Jconn/Fedora_Repo/MAAV_Projects/Spine/14v0/modules/Logic_Level_Bidirectional.sch

## EAGLE design MAAV_Projects/Spine/14v0/modules/Logic_Level_Bidirectional.sch (2014-05-22)

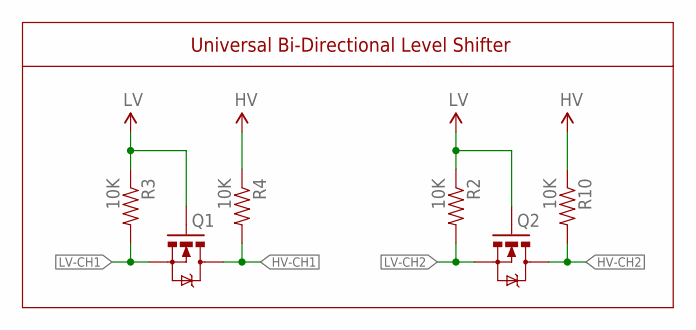
[picture p34: schematic Logic_Level_Bidirectional.sch]

Parts:
Q1: BSS138; SOT23; DIGIKEY BSS138KCT-ND
Q2: MOSFET-NCHANNELBSS138; SOT23; DIGIKEY BSS138KCT-ND
R2, R3, R4, R10: 10K; 0603-RES; DIGIKEY RMCF0603JT10K0CT-ND

Connections:
HV: R4.1, R10.1
HV-CH1: Q1.3 (D), R4.2
HV-CH2: Q2.3 (D), R10.2
LV: Q1.1 (G), Q2.1 (G), R2.1, R3.1
LV-CH1: Q1.2 (S), R3.2
LV-CH2: Q2.2 (S), R2.2

Notes on the sheet:
Universal Bi-Directional Level Shifter
