Jconn/Fedora_Repo/MAAV_Projects/Spine/14v0/modules/Motor Ouptut.sch

## EAGLE design MAAV_Projects/Spine/14v0/modules/Motor Ouptut.sch (2014-05-22)

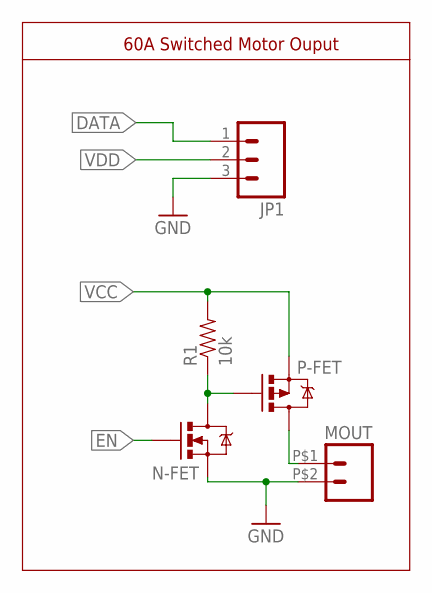
[picture p35: schematic Motor Ouptut.sch]

Parts:
JP1: M03PTH; 1X03; DIGIKEY 952-2264-ND
MOUT: MINI_FIT_JR_5569; MINI_FIT_JR
N-FET: MOSFET-NCHANNELBSS138; SOT23; DIGIKEY BSS138KCT-ND
P-FET: MOSFET_P-CHANNEL; POWERPAK_SO-8_SINGLE; DIGIKEY SI7135DP-T1-GE3CT-ND
R1: 10k; 0603-RES; DIGIKEY RMCF0603JT10K0CT-ND

Connections:
DATA: JP1.1
EN: N-FET.1 (G)
GND: JP1.3
unnamed: MOUT.P$1 (2), P-FET.P$5 (D)
unnamed: N-FET.3 (D), P-FET.P$4 (G), R1.1
unnamed: MOUT.P$2 (1), N-FET.2 (S)
VCC: P-FET.P$1 (S), R1.2
VDD: JP1.2

Notes on the sheet:
60A Switched Motor Ouput
