Jconn/Fedora_Repo/MAAV_Projects/Spine/14v0/modules/power supply.sch

## EAGLE design MAAV_Projects/Spine/14v0/modules/power supply.sch (2014-05-22)

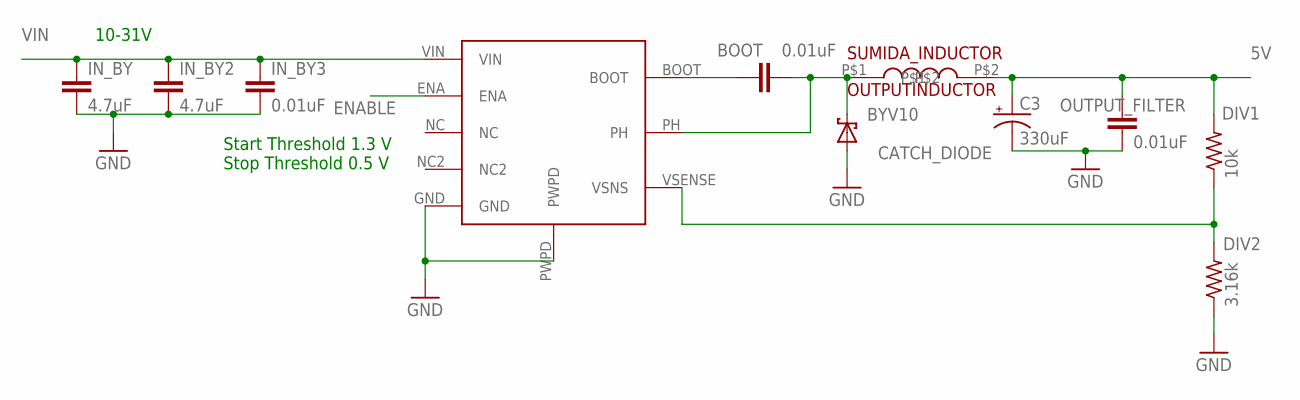
[picture p36: schematic power supply.sch]

Parts:
BOOT: 0.01uF; C0805
C3: 330uF; PANASONIC_F; DIGIKEY PCE3779CT-ND
CATCH_DIODE: BYV10; DO41-10; DIGIKEY SJPZ-N40VLCT-ND
DIV1: 10k; R0805
DIV2: 3.16k; R0805
IN_BY, IN_BY2: 4.7uF; C0805
IN_BY3: 0.01uF; C0805
OUTPUTINDUCTOR: SUMIDA_INDUCTOR; DIGIKEY 308-1333-1-ND
OUTPUT_FILTER: 0.01uF; C0805
U$1: TPS5450; TPS5450-Q1

Connections:
5V: C3.+, DIV1.2, OUTPUTINDUCTOR.P$2, OUTPUT_FILTER.1
ENABLE: U$1.ENA
GND: C3.-, CATCH_DIODE.A, DIV2.1, IN_BY.2, IN_BY2.2, IN_BY3.2, OUTPUT_FILTER.2, U$1.GND, U$1.PWPD
unnamed: BOOT.1, U$1.BOOT
unnamed: BOOT.2, CATCH_DIODE.C, OUTPUTINDUCTOR.P$1, U$1.PH
unnamed: DIV1.1, DIV2.2, U$1.VSENSE (VSNS)
VIN: IN_BY.1, IN_BY2.1, IN_BY3.1, U$1.VIN

Notes on the sheet:
10-31V
Start Threshold 1.3 V Stop Threshold 0.5 V
